PatternAgents/CPM_Shield/CPM_Shield/eagleUp/eagleUp_cpm_shield_basic_board_bottom.jpg

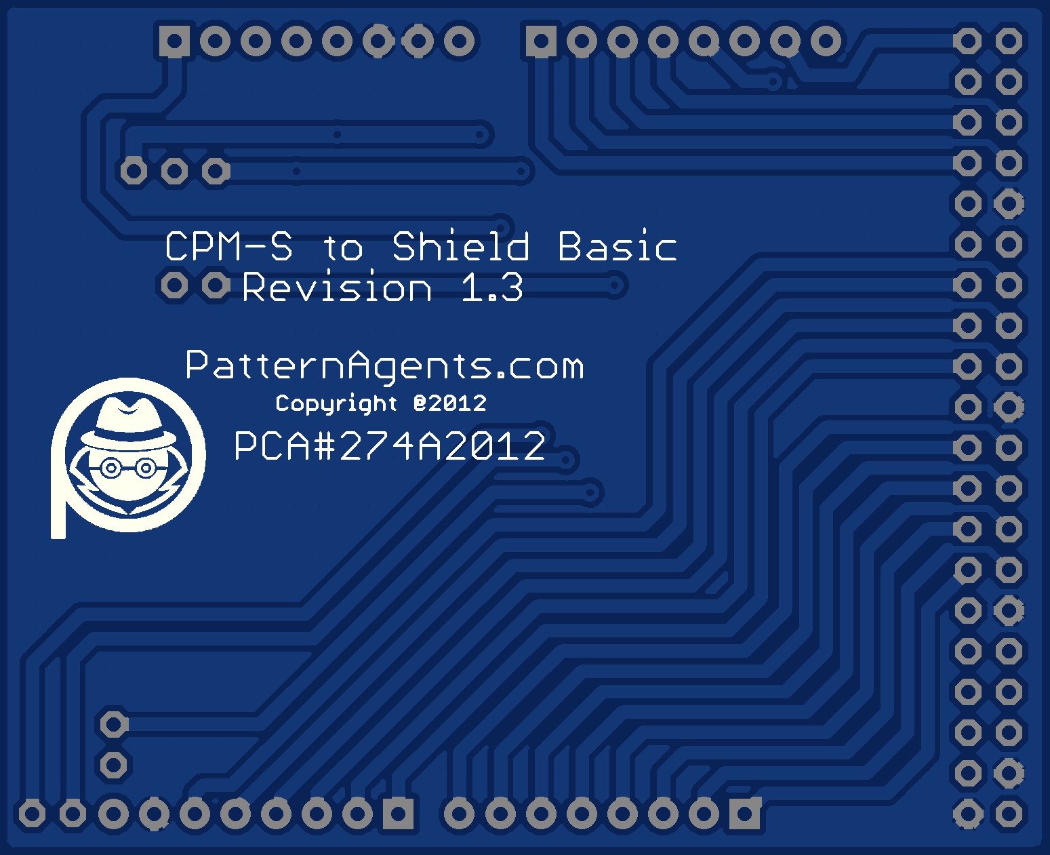
CPM_Shield/eagleUp/eagleUp_cpm_shield_basic_board_bottom.jpg
