PatternAgents/CPM_Shield/CPM_Shield/eagleUp/eagleUp_cpm_shield_basic_bottom_mask.png

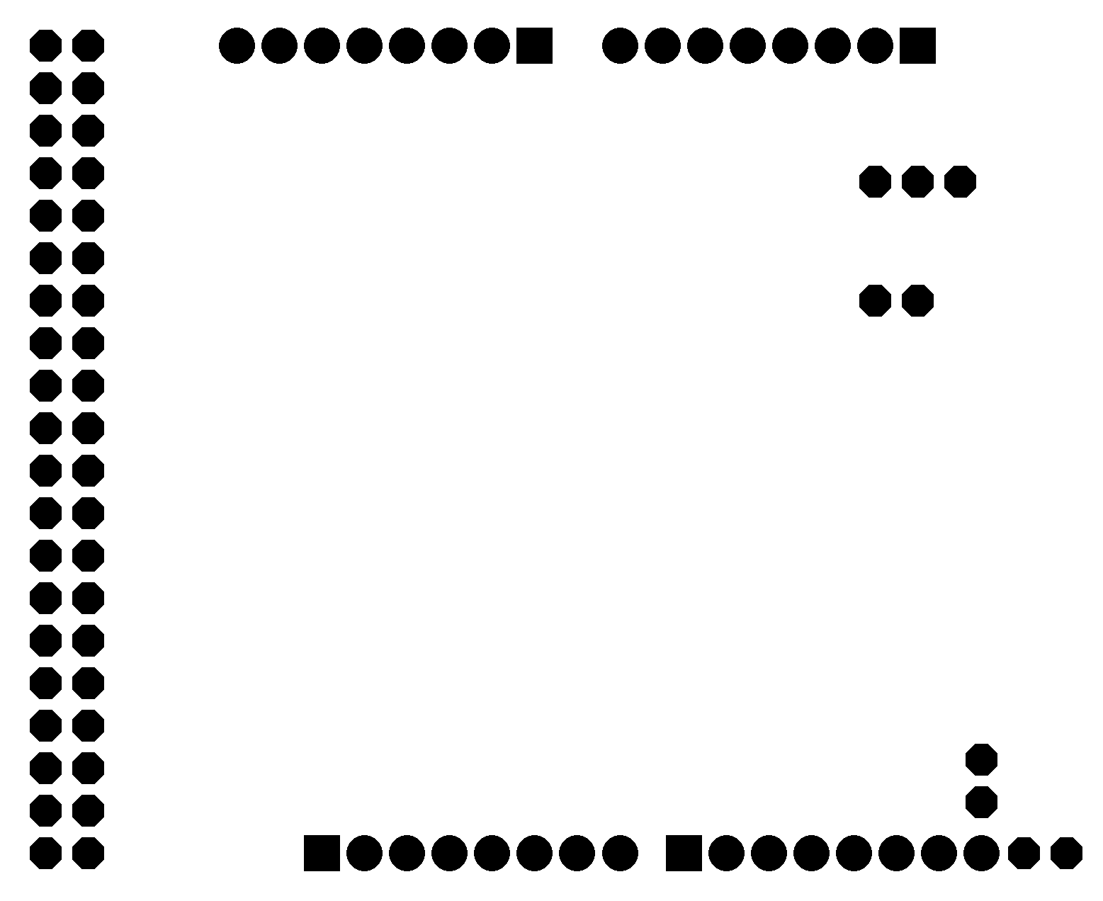
CPM_Shield/eagleUp/eagleUp_cpm_shield_basic_bottom_mask.png
