PatternAgents/CPM_Shield/CPM_Shield/eagleUp/eagleUp_cpm_shield_basic_bottom_silk.png

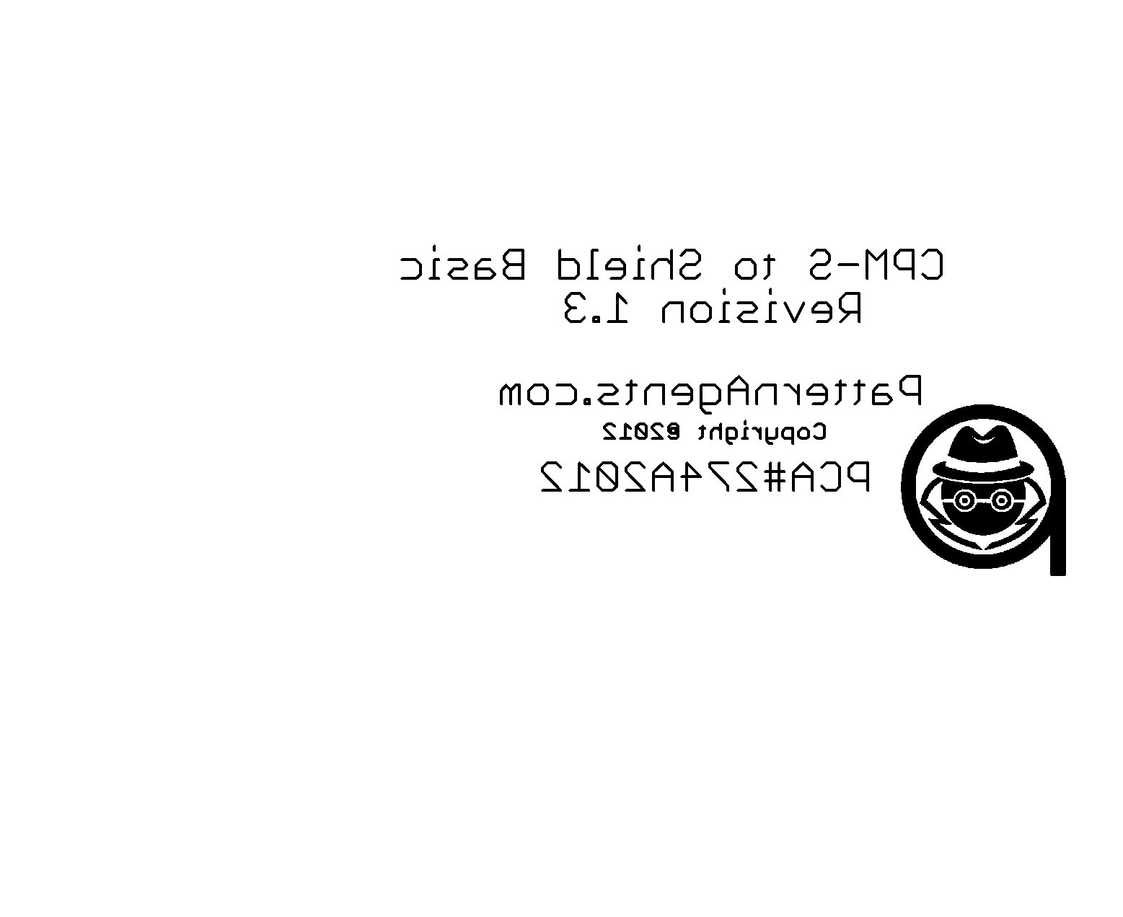
CPM_Shield/eagleUp/eagleUp_cpm_shield_basic_bottom_silk.png
