PatternAgents/CPM_Shield/CPM_Shield/eagleUp/eagleUp_cpm_shield_basic_outline.png

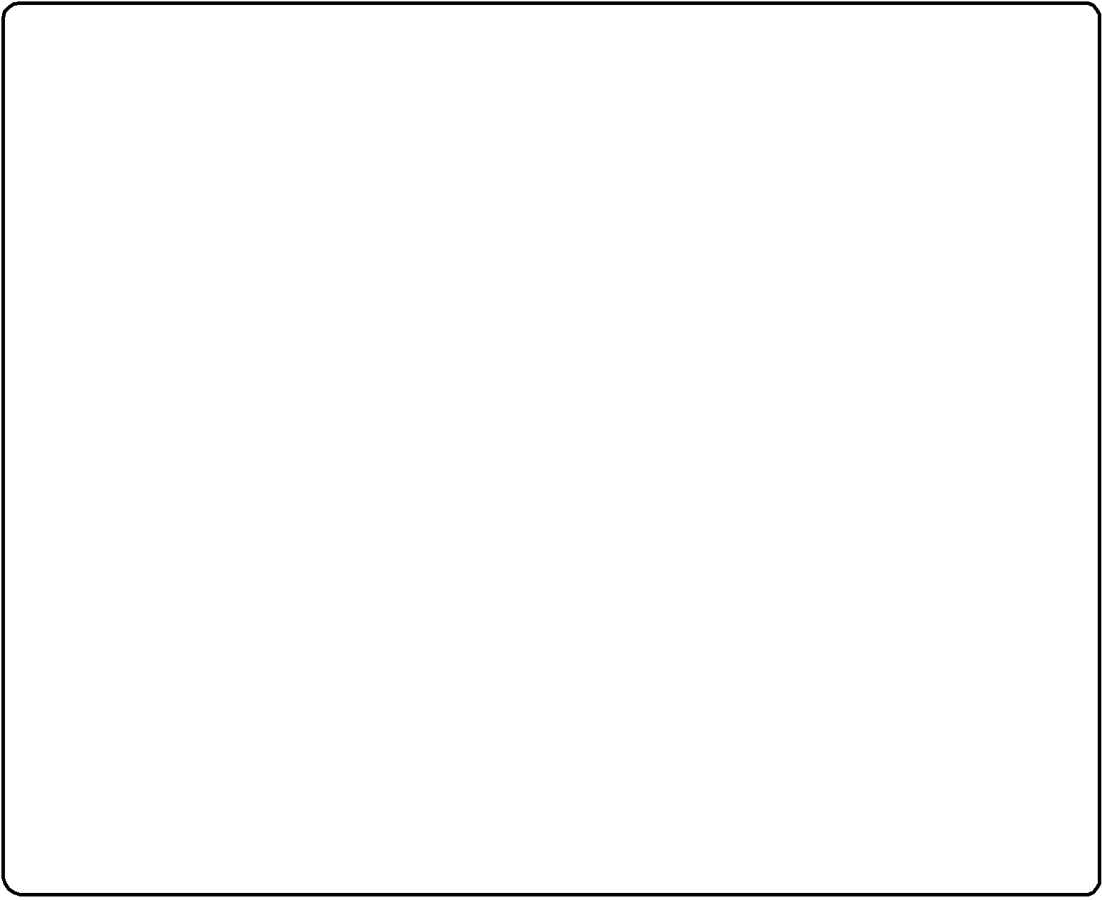
CPM_Shield/eagleUp/eagleUp_cpm_shield_basic_outline.png
