PatternAgents/CPM_Shield/CPM_Shield/images/final/hires/cpm1_kit_001B.jpg

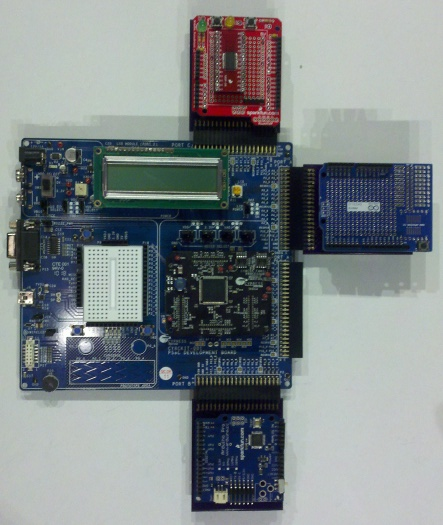
CPM_Shield/images/final/hires/cpm1_kit_001B.jpg
