PatternAgents/CPM_Shield/CPM_Shield/images/final/hires/cpm_to_shield_basic.png

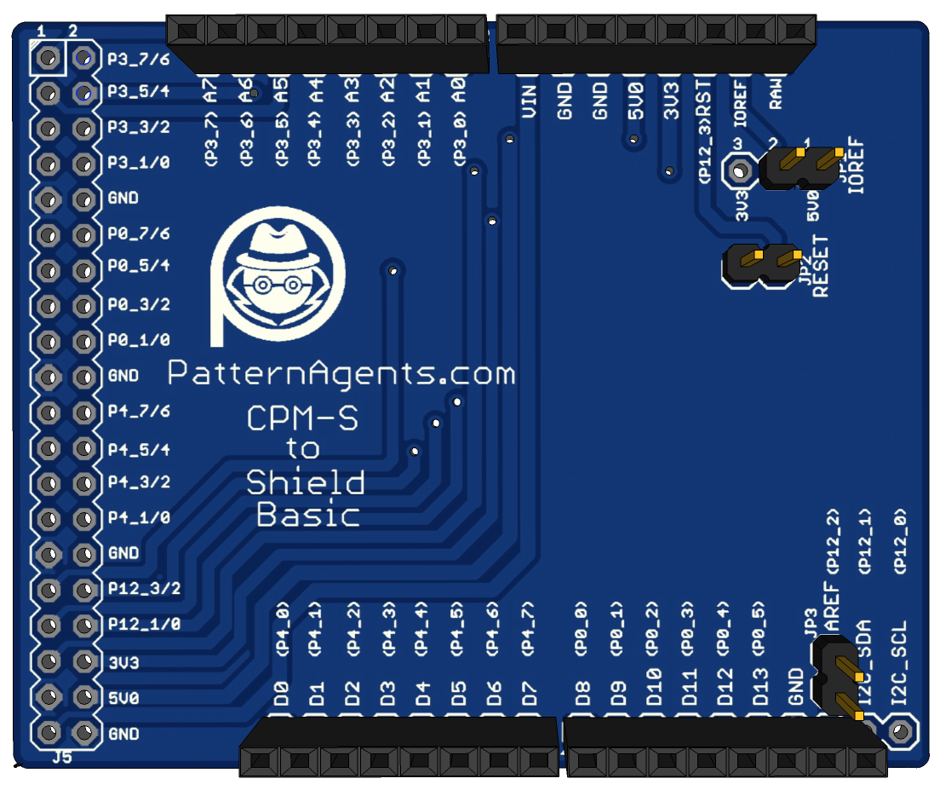
CPM_Shield/images/final/hires/cpm_to_shield_basic.png
