PatternAgents/CPM_Shield/CPM_Shield/images/final/hires/with_28xxx_SRM_board.jpg

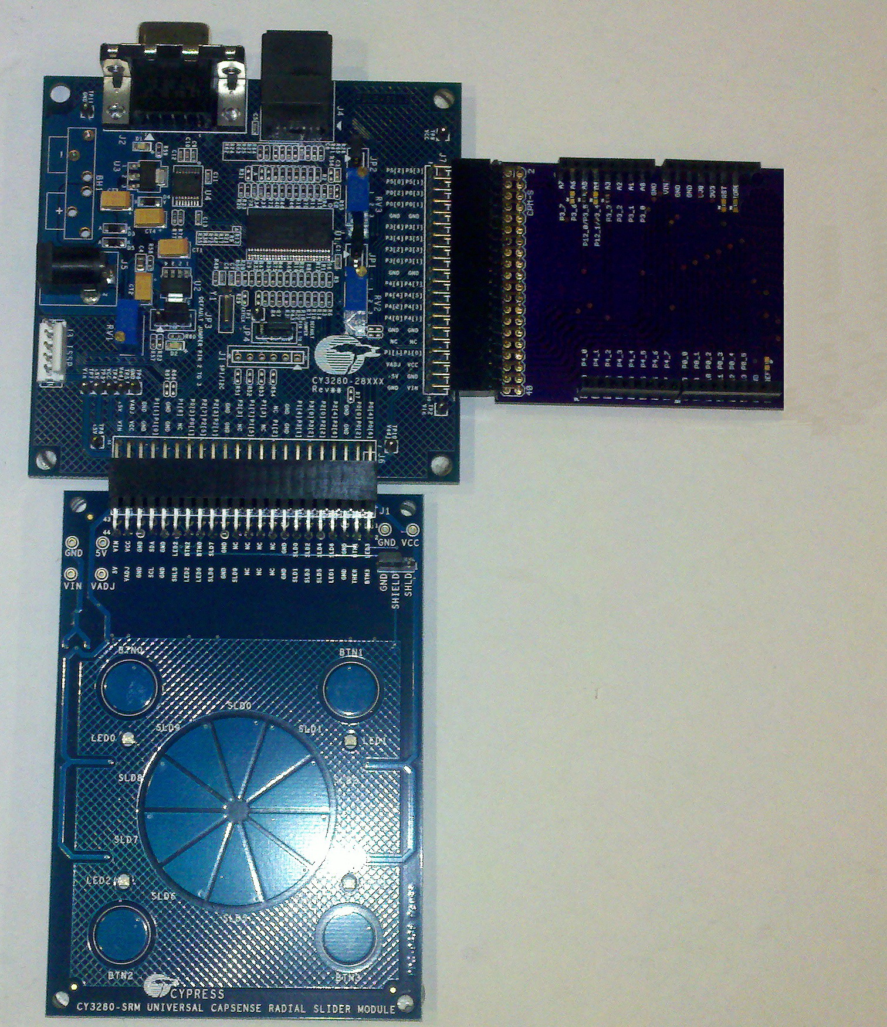
CPM_Shield/images/final/hires/with_28xxx_SRM_board.jpg
