PatternAgents/CPM_Shield/CPM_Shield/images/final/hires/with_030_board.jpg

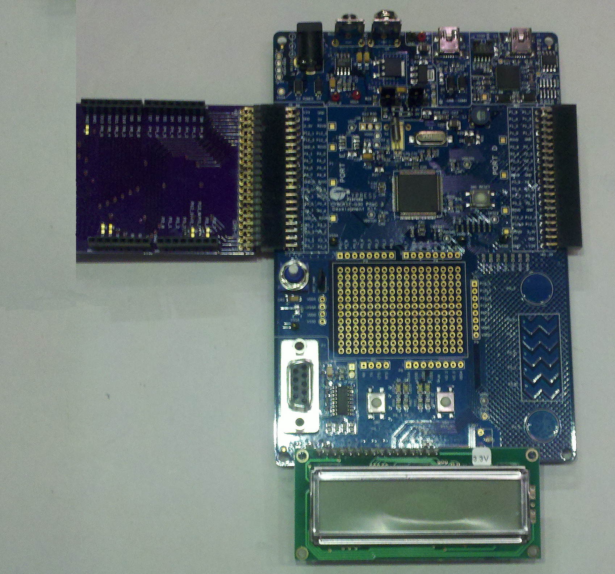
CPM_Shield/images/final/hires/with_030_board.jpg
