PatternAgents/CPM_Shield/CPM_Shield/images/final/hires/with_030_board_Port_D.jpg

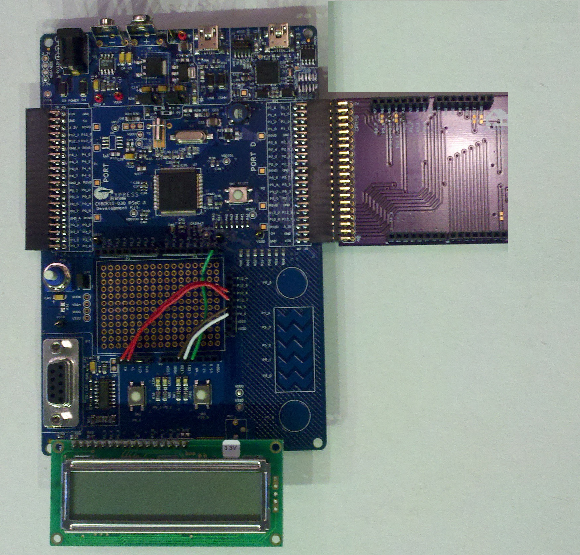
CPM_Shield/images/final/hires/with_030_board_Port_D.jpg
