PatternAgents/CPM_Shield/CPM_Shield/images/final/lores/with_030_board_SD_CARD.jpg

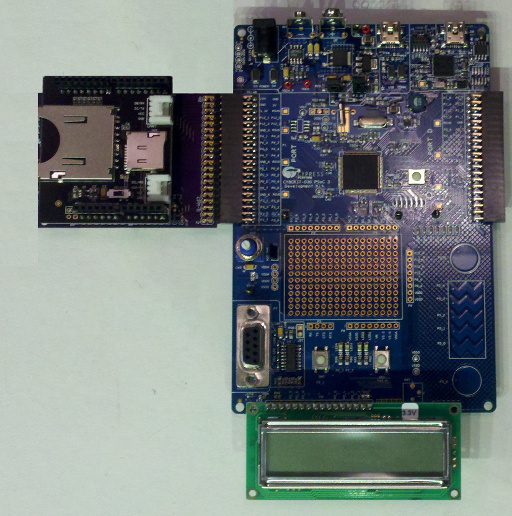
CPM_Shield/images/final/lores/with_030_board_SD_CARD.jpg
